mlab-modules/PERISTALTIC01/hw/stl/4printing/pump.stl

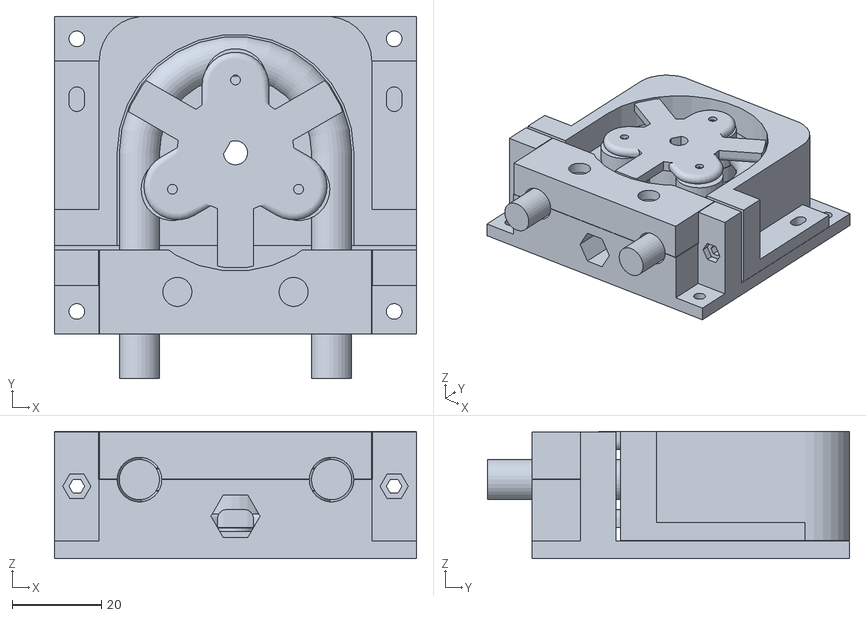
[picture p18: CAD file, 2020-04-22]
hw/stl/4printing/pump.stl
81.0 x 81.0 x 28.5
