mlab-modules/PERISTALTIC01/hw/cad/src/4printing/case_bottom.scad

include <../case-v3.scad>
assembly      = 0;   // render assembly
render_top    = 0;   // render top part
render_bottom = 1;   // render bottom part
render_side_panel = 0;   // render bottom part
