mlab-modules/PERISTALTIC01/hw/cad/src/4printing/case_top.scad

include <../case-v3.scad>
assembly      = 0;   // render assembly
render_top    = 1;   // render top part
render_bottom = 0;   // render bottom part
render_side_panel = 1;   // render side panel
