mlab-modules/PERISTALTIC01/hw/cad/src/4printing/rotor_base.scad

include <../pump-v3.scad>
//@set_slicing_parameter(fill_density, 100%)
assemble = 0;
halfcut = 0;
moved_apart = 0;
partNum = 4;
