mlab-modules/PERISTALTIC01/hw/cad/src/4printing/stator_cover.scad

include <../pump-v3.scad>
assemble = 0;
halfcut = 0;
moved_apart = 0;
partNum = 3;
