mlab-modules/PERISTALTIC01/hw/cad/src/assembly/pump.scad

include <../pump-v3.scad>
assemble = 1;
halfcut = 0;
moved_apart = 0;
