mlab-modules/PERISTALTIC01/doc/src/img/4printing/case_bottom.png

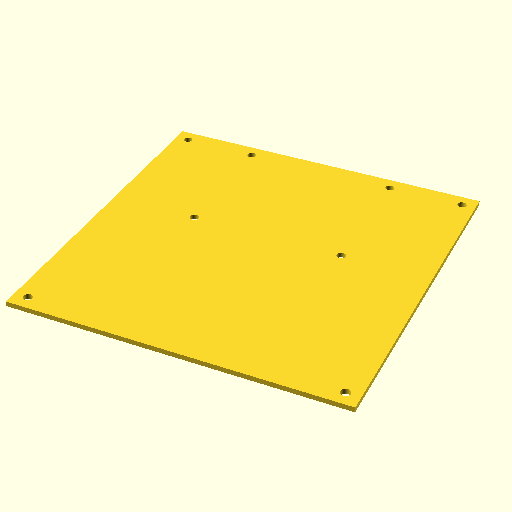
doc/src/img/4printing/case_bottom.png
