mlab-modules/PERISTALTIC01/doc/src/img/4printing/rotor_base.png

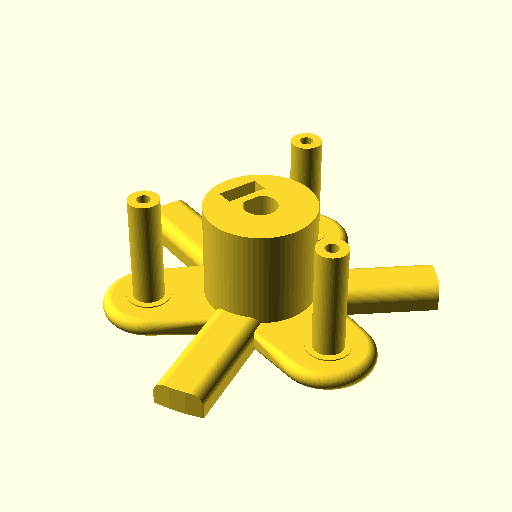
doc/src/img/4printing/rotor_base.png
