mlab-modules/PERISTALTIC01/doc/src/img/4printing/rotor_cover.png

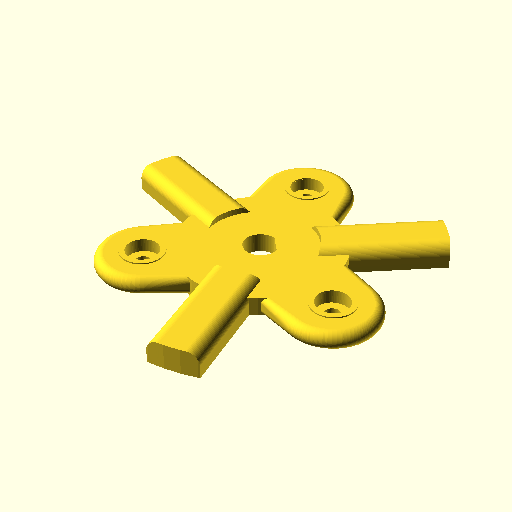
doc/src/img/4printing/rotor_cover.png
