mlab-modules/PERISTALTIC01/doc/src/img/4printing/stator_base.png

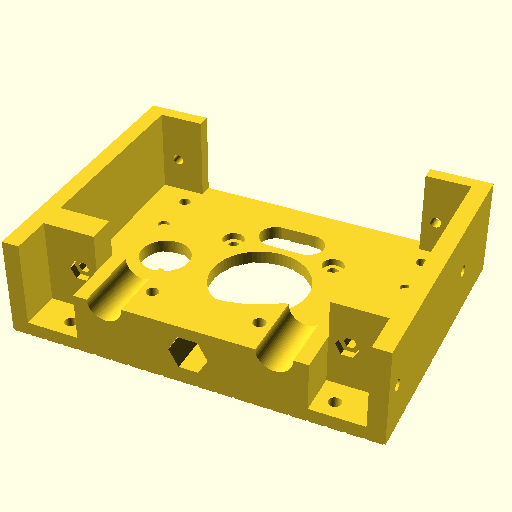
doc/src/img/4printing/stator_base.png
