mlab-modules/PERISTALTIC01/doc/src/img/4printing/stator_cover.png

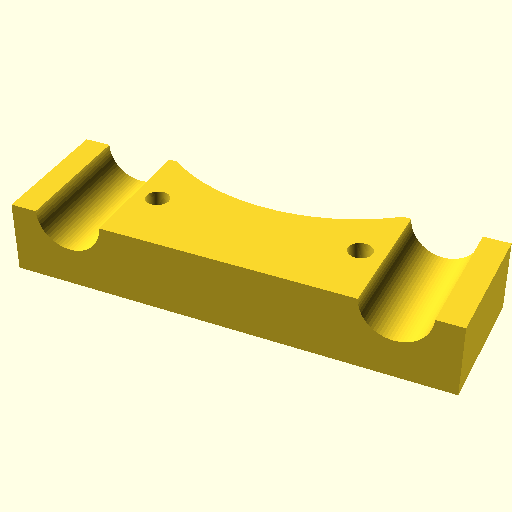
doc/src/img/4printing/stator_cover.png
